MaroshCZ/Power-Supply-USB-C/STM32G0_USBPD_Sink_1.2/Application/app.c

/*
 * app.c
 *
 *  Created on: Apr 29, 2024
 *      Author: Jan Mareš
 */


#include "main.h"
#include "app.h"
#include "max7219.h"
#include "usbpd_def.h"
#include "usbpd_dpm_user.h"
#include "usbpd_pwr_user.h"
#include "usbpd_user_services.h"
#include "string.h"
#include "stdio.h"
#include "stdbool.h"
#include <stm32g0xx_ll_adc.h>

#include "usb_device.h"
#include "usbd_cdc_if.h"
#include <usbpd_trace.h>

int32_t fullyCompensatedVoltageV;
int32_t currentCompensatedVoltageV;
int32_t compVoltageV;
int32_t currentErrorV;
uint64_t term1V;
uint64_t term2V;
int64_t	voltageErrorV;
int32_t voltageErrorRoundedV;

int32_t BSP_USBPD_PWR_VBUSGetCurrentOCP(uint32_t Instance, int32_t *pCurrentOCP);
int32_t BSP_PWR_VBUSGetCurrentOCP(uint32_t PortId);

//Variables declaration
int dac_value = 500;

USBPD_DPM_SNKPowerRequestDetailsTypeDef powerRequestDetails;

__IO uint16_t aADCxConvertedValues[ADC_NUM_OF_SAMPLES] = {0};

//USB communication
uint8_t usb_buffer[64]; //in C, array automaticaly decays to pointer to first element uint8_t*

uint8_t *getUSBbuffer(void) {
	return usb_buffer;
}


//Initialize button event and time struct
SystemEvents_TypeDef systemEvents = {0};
BtnPressTimes_TypeDef btnPressTimes = {0};
volatile uint32_t debouncedPins = 0;  // Bitmask for tracking debounced buttons

//Init stateMachine struct
StateMachine_TypeDef stateMachine = {
		.currentState = STATE_INIT,
		.comState = STATE_CLOSED,
		.lockMode = UNLOCKED,
		.OCPMode = OCP_ENABLED,
		.lockLedState = LED_ON,
		.pwrMode = MODE_FIXED,
		.encoder = {
				.selDigit = 2,
				.increment = 10    // Default increment
			}
};

//Init SINKData struct
SINKData_HandleTypeDef SNK_data = {
	.voltageMin = 500, //initial min voltage
	.voltageSet = 500, //initial value to display
	.voltageMax = 500, //initial max voltage
	.currentSet = 1000, //initial value to display
	.awdgTresholdSet = 744, //set initial OCP to 1A
	.currentMin = 0,
	.currentOCPSet = 1000,
	.selMethod = PDO_SEL_METHOD_MAX_CUR,
	.hasAPDO = false,
	.srcProfiles[0].profileType = UNKNOWN,
	.requestOngoing = false
};

SINKData_HandleTypeDef *getSNK_data(void) {
	return &SNK_data;
}

// Define the pointer to the struct
SINKData_HandleTypeDef *dhandle = &SNK_data;
StateMachine_TypeDef *sm = &stateMachine;
SystemEvents_TypeDef *events = &systemEvents;


// Callback when ADC conversion is complete
void HAL_ADC_ConvCpltCallback(ADC_HandleTypeDef *hadc)
{
  //HAL_GPIO_TogglePin(LED_USER_GPIO_Port, LED_USER_Pin);
}

// Callback when ADWG2 (CH7 ISENSE) goes out of range
void HAL_ADCEx_LevelOutOfWindow2Callback(ADC_HandleTypeDef *hadc) {
	systemEvents.awdgEvent = true;
	//Disable output
	HAL_GPIO_WritePin(RELAY_ON_OFF_GPIO_Port, RELAY_ON_OFF_Pin, GPIO_PIN_RESET);
}

/**
 * Update ADC CH3 AWD Treshold
 * Possibility to update parameters on the fly (read more in HAL_ADC_AnalogWDGConfig declaration)
 * Full config and AWD init in main.c
 */
void Update_AWD_Thresholds(uint32_t low, uint32_t high, uint32_t adc_watchdog) {
		// Just update the thresholds for an already configured AWD
		ADC_AnalogWDGConfTypeDef AnalogWDGConfig = {0};
		AnalogWDGConfig.WatchdogNumber = adc_watchdog; // Specify which AWD you're updating
		AnalogWDGConfig.HighThreshold = high;
		AnalogWDGConfig.LowThreshold = low;
		if (HAL_ADC_AnalogWDGConfig(&hadc1, &AnalogWDGConfig) != HAL_OK)
		{
		    Error_Handler();
		}
}
/*
 * Initialization function
 */
void app_init(void){
	//TIM4 initialization
	HAL_TIM_Base_Start(&htim4);

	//TIM7 initialization
	LL_TIM_ClearFlag_UPDATE(TIM7); //Clear update flag on TIMER7
	LL_TIM_EnableIT_UPDATE(TIM7); //Enable interrupt generation when timer goes to max value and UPDATE event flag is set
	//LL_TIM_ClearFlag_UPDATE(TIM7); //Clear update flag on TIMER7

	//TIM14 initialization
	LL_TIM_DisableIT_UPDATE(TIM14); //Enable interrupt generation when timer goes to max value and UPDATE event flag is set
	LL_TIM_ClearFlag_UPDATE(TIM14); //Clear update flag on TIMER14

	//TIM14 initialization
	LL_TIM_DisableIT_UPDATE(TIM15); //Enable interrupt generation when timer goes to max value and UPDATE event flag is set
	LL_TIM_ClearFlag_UPDATE(TIM15); //Clear update flag on TIMER14

	//TIM3 initialization of encoder
	HAL_TIM_Encoder_Start_IT(&htim3, TIM_CHANNEL_ALL);
	uint32_t maxCounterValue = __HAL_TIM_GET_AUTORELOAD(&htim3); // Get the max value
	__HAL_TIM_SET_COUNTER(&htim3, maxCounterValue / 2); // Set the counter to half of the max value to avoid shift from 0 -> max value
	sm->encoder.curValue = __HAL_TIM_GET_COUNTER(&htim3)/4;
	sm->encoder.prevValue = sm->encoder.curValue;

	//Init DAC
	HAL_DAC_Start(&hdac1, DAC_CHANNEL_1);
	HAL_DAC_SetValue(&hdac1, DAC_CHANNEL_1, DAC_ALIGN_12B_R, dac_value);

	//Wait for hardware initialization and then turn DB to HIGH (according to TCPP01-M12 datasheet 6.5)
	HAL_Delay(200);
	HAL_GPIO_WritePin(DB_OUT_GPIO_Port, DB_OUT_Pin, GPIO_PIN_SET);

	//Calibrate and start ADC sensing with DMA
	HAL_ADCEx_Calibration_Start(&hadc1);
	HAL_ADC_Start_DMA(&hadc1, (uint32_t*)&aADCxConvertedValues, ADC_NUM_OF_SAMPLES);

	//Set initial OCP treshold
	Update_AWD_Thresholds(0, dhandle->awdgTresholdSet, ADC_ANALOGWATCHDOG_2); //~1A
	HAL_GPIO_WritePin(LED_USER_GPIO_Port, LED_USER_Pin, GPIO_PIN_SET);

	//Init 7 segment display
	max7219_Init( SEGMENT_DISP_INTENSIVITY );
	max7219_Decode_On();

	//HAL_GPIO_WritePin(OCP_RESET_GPIO_Port, OCP_RESET_Pin, GPIO_PIN_SET);
}


/*
 * Main loop function
 */
void app_loop(void) {
	// Process button events
	processSystemEvents();

	// Update lock/ocp LED
	updateLockLED();

	// Run the state machine
	runStateMachine();

	// Reset button states after processing
	stateMachine.outputBtnPressed = false;
	stateMachine.lockBtnPressed = false;
	stateMachine.lockBtnLongPressed = false;
	stateMachine.voltageCurrentBtnPressed = false;
	stateMachine.voltageCurrentBtnLongPressed = false;
	stateMachine.rotaryBtnPressed = false;
	stateMachine.encoderTurnedFlag = false;
	stateMachine.stateTimeoutFlag = false;
	stateMachine.periodicCheckFlag = false;
	stateMachine.encoderTurnedFlag = false;
	stateMachine.awdgTriggeredFlag = false;
}

/*
 * Main function for state machine
 */
void runStateMachine(void) {
	// Process events and transitions
	switch (sm->currentState) {
		case STATE_OFF:
			//handleOffState();
			break;
		case STATE_INIT:
			handleInitState();
			break;
		case STATE_IDLE:
			handleIdleState();
			break;
		case STATE_ACTIVE:
			handleActiveState();
			break;
		case STATE_ERROR:
			//handleErrorState();
			break;
		case STATE_SET_VALUES:
			handleSetValuesState();
			break;
		default:
			// Error handling
			sm->currentState = STATE_ERROR;
			//sm->errorCode = ERROR_INVALID_STATE;
			break;
	}

}

/*
 * Define Callbacks and ISR
 */

//BTN ISR to set event flags
void HAL_GPIO_EXTI_Falling_Callback(uint16_t GPIO_Pin) {
    if (GPIO_Pin == SW1_TOGGLE_I_V_Pin) {
        btnPressTimes.voltageCurrentBtn = HAL_GetTick();
        systemEvents.btnPressEvent = true;
        //EXTI->IMR1 &= ~(EXTI_IMR1_IM2);
    } else if (GPIO_Pin == SW2_DEBUG_BTN_Pin) {
        btnPressTimes.lockBtn = HAL_GetTick();
        systemEvents.btnPressEvent = true;
        //EXTI->IMR1 &= ~(EXTI_IMR1_IM4);
    } else if (GPIO_Pin == SW3_OFF_ON_Pin) {
        systemEvents.outputBtnEvent = true;
        //EXTI->IMR1 &= ~(EXTI_IMR1_IM1);
    } else if (GPIO_Pin == ENC_TOGGLE_UNITS_Pin) {
        systemEvents.rotaryBtnEvent = true;
        //EXTI->IMR1 &= ~(EXTI_IMR1_IM8);
    }

    // Store the pressed button in bitmask for tracking debounce
    debouncedPins |= GPIO_Pin;
    // Mask the interrupt for this button
    EXTI->IMR1 &= ~GPIO_Pin;

    // Start debounce timer
    TIM7->ARR = DEBOUNCE_TIME_MS;
    LL_TIM_SetCounter(TIM7, 0);
    LL_TIM_EnableCounter(TIM7);
}

/*
 * Define Callbacks and ISR
 */

//BTN ISR to set event flags
void HAL_GPIO_EXTI_Rising_Callback(uint16_t GPIO_Pin) {

	if (systemEvents.btnPressEvent == true) {
		uint32_t releaseTime = HAL_GetTick();

		// Decide between long/short presses
		if (GPIO_Pin == SW1_TOGGLE_I_V_Pin) {
			if ((releaseTime - btnPressTimes.voltageCurrentBtn) > 1000) {
				systemEvents.voltageCurrentBtnLongEvent = true;
			} else {
				systemEvents.voltageCurrentBtnEvent = true;
			}

		} else if (GPIO_Pin == SW2_DEBUG_BTN_Pin) {

			if ((releaseTime - btnPressTimes.lockBtn) > 1000) {
				systemEvents.lockBtnLongEvent = true;
			} else {
				systemEvents.lockBtnEvent = true;
			}
		} else {
			return;
		}

		// Start debounce timer
		TIM7->ARR = DEBOUNCE_TIME_MS;
		LL_TIM_SetCounter(TIM7, 0);
		LL_TIM_EnableCounter(TIM7);

		// Reset btnPressEvent
		systemEvents.btnPressEvent = false;

		// Store the pressed button in bitmask for tracking debounce
		debouncedPins |= GPIO_Pin;
		// Mask the interrupt for this button
		EXTI->IMR1 &= ~GPIO_Pin;
	}
}

//TIM capture callback
void HAL_TIM_IC_CaptureCallback(TIM_HandleTypeDef *htim) {
    if (htim->Instance == TIM3) {
    	systemEvents.encoderTurnEvent = true;
    }
}

/*
 * Timer7 interrupt routine for button debouncing
 */
void TIM7_ISR(void){
	//Clear TIM update flag and stop timer
	LL_TIM_ClearFlag_UPDATE(TIM7);
	LL_TIM_DisableCounter(TIM7);

	EXTI->IMR1 |= debouncedPins; // Unmask debounced pins
	EXTI->FPR1 = debouncedPins; // clear falling edge interrupt
	EXTI->RPR1 = debouncedPins; // clear rising edge interrupt

	// Reset the bitmask after unmasking
	debouncedPins = 0;

}

/*
 * TIM14 interrupt routine for periodic check inside states
 *
 */
void TIM14_ISR(void) {
	if (LL_TIM_IsActiveFlag_UPDATE(TIM14)) {
		// Clear the update interrupt flag
		LL_TIM_ClearFlag_UPDATE(TIM14);

		// Handle periodic check for ACTIVE state
		systemEvents.periodicCheckEvent = true;
		//Reset CNT value
		LL_TIM_SetCounter(TIM14, 0);

		//Start timer again
		LL_TIM_EnableCounter(TIM14);
	}
}

/*
 * TIM15 interrupt routine for timeouts of states
 *
 */
void TIM15_ISR(void) {
	if (LL_TIM_IsActiveFlag_UPDATE(TIM15)) {
		// Clear the update interrupt flag
		LL_TIM_ClearFlag_UPDATE(TIM15);

		// Handle periodic check for ACTIVE state
		systemEvents.stateTimeoutEvent = true;
		//Reset CNT value
		//LL_TIM_DisableCounter(TIM15);  // Stop the timer after timeout
	}
}

/*
 * Define Process functions
 */
// Process button events in the main loop (Convert hardware events into logical events)
void processButtonEvents(void) {
    if (events->outputBtnEvent) {
    	//Reset btn event flag
        events->outputBtnEvent = false;
        sm->outputBtnPressed = true;

    } else if (events->voltageCurrentBtnEvent) {
    	events->voltageCurrentBtnEvent = false;
    	sm->voltageCurrentBtnPressed = true;
    } else if (events->voltageCurrentBtnLongEvent) {
       	events->voltageCurrentBtnLongEvent = false;
       	sm->voltageCurrentBtnLongPressed = true;

       	// Toggle pwrMode
       	if (sm->pwrMode == MODE_FIXED) {
       		sm->pwrMode = MODE_APDO;
       	} else {
       		sm->pwrMode = MODE_FIXED;
       	}

    } else if (events->lockBtnEvent) {
    	events->lockBtnEvent = false;

    	if (sm->lockMode == UNLOCKED) {
    		sm->lockBtnPressed = true;
    		int isense_Vtrip_mV;
    		int isense_rawADCtrip;

			//Toggle OCP mode
			switch(sm->OCPMode) {
				case OCP_DISABLED:
					sm->OCPMode = OCP_ENABLED;

					//Set lock LED
					//HAL_GPIO_WritePin(LED_LOCK_GPIO_Port, LED_LOCK_Pin, GPIO_PIN_SET);

					//Update AWD limits
					isense_Vtrip_mV = (dhandle->currentSet *G_SENSE*R_SENSE_MOHMS)/1000; // mV  (mA * mOhms * Gain)
					isense_rawADCtrip = (isense_Vtrip_mV *4095) / VDDA_APPLI; //value for AWD treshold
					dhandle->awdgTresholdSet = isense_rawADCtrip;
					Update_AWD_Thresholds(0, isense_rawADCtrip, ADC_ANALOGWATCHDOG_2);
					break;
				case OCP_ENABLED:
					sm->OCPMode = OCP_DISABLED;

					//Reset lock LED
					//HAL_GPIO_WritePin(LED_LOCK_GPIO_Port, LED_LOCK_Pin, GPIO_PIN_RESET);

					//If OCP disabled by user, set it to source max current
					isense_Vtrip_mV = (dhandle->currentMax *G_SENSE*R_SENSE_MOHMS)/1000; // mV  (mA * mOhms * Gain)
					isense_rawADCtrip = (isense_Vtrip_mV *4095) / VDDA_APPLI; //value for AWD treshold
					dhandle->awdgTresholdSet = isense_rawADCtrip;
					Update_AWD_Thresholds(0, isense_rawADCtrip, ADC_ANALOGWATCHDOG_2);

					//__HAL_ADC_DISABLE_IT(&hadc1, ADC_IT_AWD2); can be also used to write bit but
					//only when ADSTART bit is cleared to 0 (this ensures that no conversion is ongoing).
					break;
			}
    	}

    } else if (events->lockBtnLongEvent) {
    	events->lockBtnLongEvent = false;
    	sm->lockBtnLongPressed = true;

    	if (sm->lockMode == LOCKED) {
    		sm->lockMode = UNLOCKED;

    		//Drive lock LED
    		//HAL_GPIO_WritePin(LED_LOCK_GPIO_Port, LED_LOCK_Pin, GPIO_PIN_RESET);
    		HAL_GPIO_WritePin(LED_USER_GPIO_Port, LED_USER_Pin, GPIO_PIN_RESET);


    		// Mask buttons except OUT
    		EXTI->IMR1 |= EXTI_IMR1_IM8; //unmask ENCbtn
    		EXTI->IMR1 |= EXTI_IMR1_IM2; //unmask SW1 I/V
    	} else {
    		sm->lockMode = LOCKED;

    		// Drive lock LED
    		//HAL_GPIO_WritePin(LED_LOCK_GPIO_Port, LED_LOCK_Pin, GPIO_PIN_SET);
    		HAL_GPIO_WritePin(LED_USER_GPIO_Port, LED_USER_Pin, GPIO_PIN_SET);

    		// Unmask buttons except OUT
    		EXTI->IMR1 &= ~(EXTI_IMR1_IM2); // mask SW1 I/V
    		EXTI->IMR1 &= ~(EXTI_IMR1_IM8); // mask ENCbtnt
    	}

    } else if (events->rotaryBtnEvent) {
    	// Reset btn event flag
    	events->rotaryBtnEvent = false;
		sm->rotaryBtnPressed = true;

    }
}

void processLockLedState(void) {
	 if (sm->OCPMode == OCP_DISABLED && sm->lockMode == UNLOCKED)
		sm->lockLedState = LED_OFF;
	else if (sm->OCPMode == OCP_ENABLED && sm->lockMode == UNLOCKED)
		sm->lockLedState = LED_ON;
	else if (sm->OCPMode == OCP_DISABLED && sm->lockMode == LOCKED)
		sm->lockLedState = LED_BLINK_SLOW;
	else if (sm->OCPMode == OCP_ENABLED && sm->lockMode == LOCKED)
		sm->lockLedState = LED_BLINK_FAST;
}


// Main system event processor that calls specialized handlers
void processSystemEvents(void) {
    // Process different event types using specialized functions
    processButtonEvents();

    // Process LockLed state based on decision matrix
    processLockLedState();


    // Process encoder actions
    if (events->encoderTurnEvent) {
    	sm->encoderTurnedFlag = true;
    	events->encoderTurnEvent = false;
    }
    // Process timeout of TIM15
    if (events->stateTimeoutEvent) {
		sm->stateTimeoutFlag= true;
		events->stateTimeoutEvent = false;
	}
    // Process periodic check of TIM14
	if (events->periodicCheckEvent) {
		sm->periodicCheckFlag= true;
		events->periodicCheckEvent = false;
	}
    // Process AWDG events
    if (events->awdgEvent) {
        events->awdgEvent = false;
        sm->awdgTriggeredFlag = true;
    }
}

/**
 * @brief Handle COM port status changes. Drive indicator LED and disable/enable button actions.
 *
 * @param host_com_port_open: is a bit value from CDC_Control_FS() case CDC_SET_CONTROL_LINE_STATE
 */
void handleCOMportstatus(uint8_t host_com_port_open){
	 static bool entryDone = false;
	 if (host_com_port_open == 1 && !entryDone) {
		 //Set COM state to OPEN
		 sm->comState = STATE_OPEN;
		 //Set default state timeout to 4000;
		 sm->timeoutCounter = 1500;

		 //Drive lock LED
		 //HAL_GPIO_WritePin(LED_LOCK_GPIO_Port, LED_LOCK_Pin, GPIO_PIN_SET);
		 HAL_GPIO_WritePin(LED_USER_GPIO_Port, LED_USER_Pin, GPIO_PIN_SET);

		 //Disable BTN interrupts
		 EXTI->IMR1 &= ~(EXTI_IMR1_IM2); //SW1
		 EXTI->IMR1 &= ~(EXTI_IMR1_IM4); //SW2
		 EXTI->IMR1 &= ~(EXTI_IMR1_IM1); //SW3
		 EXTI->IMR1 &= ~(EXTI_IMR1_IM8); //ENC btn

		 entryDone = true;

	 // Adding && entryDone is vital since it would otherwise entry this statement during debug
	 } else if (host_com_port_open == 0 && entryDone) {
		 sm->comState = STATE_CLOSED;

		 //Reset lock LED
		 //HAL_GPIO_WritePin(LED_LOCK_GPIO_Port, LED_LOCK_Pin, GPIO_PIN_RESET);
		 HAL_GPIO_WritePin(LED_USER_GPIO_Port, LED_USER_Pin, GPIO_PIN_RESET);

		 //Unmask exti line 1, 2 and 3
		 EXTI->IMR1 |= EXTI_IMR1_IM8; //unmask exti line 8
		 EXTI->IMR1 |= EXTI_IMR1_IM4; //unmask exti line 4
		 EXTI->IMR1 |= EXTI_IMR1_IM2; //unmask exti line 2
		 EXTI->IMR1 |= EXTI_IMR1_IM1; //unmask exti line 1

		 //If COM closed return savely to IDLE
		 sm->currentState = STATE_IDLE;

		 entryDone = false;
	 }
}

/**
 * @brief Clean specified delimiter from string array.
 *
 * @param input: Input string to be cleaned
 * @param output: Destination buffer for cleaned string
 * @param delimiter: Delimiter character(s) to be removed
 */
void cleanString(const char* input, char* output, const char* delimiter) {
    char temp[128];  // Temporary buffer for safe modification
    strncpy(temp, input, sizeof(temp) - 1);
    temp[sizeof(temp) - 1] = '\0';  // Ensure null-termination

    char* token = strtok(temp, delimiter);
    output[0] = '\0';  // Start with an empty output string

    while (token != NULL) {
        strcat(output, token);  // Append token to output
        token = strtok(NULL, delimiter);
    }
}


/**
 * @brief Process USB commands received from host.
 *
 * @param command: Pointer to command buffer
 * @param length: Length of the command
 *
 * Handles various commands for power supply control including:
 * - OCP (Over-Current Protection) enable/disable
 * - Voltage and current settings
 * - Output enable/disable
 * - Query commands for device status
 */
void processUSBCommand(uint8_t* command, uint32_t length)
{
	// Verify device has Adjustable Power Delivery Object capability
    // If only fixed profiles available, abort communication
	if (dhandle->hasAPDO == true) {
		sm->pwrMode = MODE_APDO;
	}
	else {
		return;
	}

	// Null-terminate the command to ensure string functions work properly
	command[length] = '\0';

	// Make a copy for tokenization to preserve original command
	char cmd_copy[64] = {0};
	strncpy(cmd_copy, (char*)command, sizeof(cmd_copy)-1);

	// Remove whitespace characters
	char cmd_trimmed[64];
	cleanString(cmd_copy, cmd_trimmed, " ");

	// Extract command part (everything up to ":" )
	char* cmd_part = strtok(cmd_trimmed, ":");
	char* params = NULL; // Will hold the parameter value after the colon

	// Parameters start after the delimiter
	if (cmd_part != NULL && strlen(cmd_part) < length) {
		params = strtok(NULL, ":");  // Get remaining part after ':'
	}

	//Create buffer for response mesage
	char response[64];

	// Process different command types
    if (strcmp(cmd_part, "OCP1") == 0)
    {
    	snprintf(response, sizeof(response), "OCP enabled\r\n");

        sm->OCPMode = OCP_ENABLED;

		// Update Analog Watchdog limits for over-current detection
		int isense_Vtrip_mV = (dhandle->currentSet *G_SENSE*R_SENSE_MOHMS)/1000; // mV  (mA * mOhms * Gain)
		int isense_rawADCtrip= (isense_Vtrip_mV *4095) / VDDA_APPLI; //value for AWD treshold
		Update_AWD_Thresholds(0, isense_rawADCtrip, ADC_ANALOGWATCHDOG_2);
    }
    else if (strcmp(cmd_part, "OCP0") == 0)
    {
    	snprintf(response, sizeof(response), "OCP disabled\r\n");

        sm->OCPMode = OCP_DISABLED;
        int isense_Vtrip_mV = (dhandle->currentMax *G_SENSE*R_SENSE_MOHMS)/1000; // mV  (mA * mOhms * Gain)
        int isense_rawADCtrip = (isense_Vtrip_mV *4095) / VDDA_APPLI; //value for AWD treshold
        dhandle->awdgTresholdSet = isense_rawADCtrip;
        Update_AWD_Thresholds(0, isense_rawADCtrip, ADC_ANALOGWATCHDOG_2);

        // Set Analog Watchdog to disabled threshold
		Update_AWD_Thresholds(0, OCP_DISABLED_HT, ADC_ANALOGWATCHDOG_2);
    }
    else if (strcmp(cmd_part, "VSET1") == 0)
    {
    	// Set voltage mode and update voltage setting
    	sm->rotaryBtnPressed = true;
    	sm->setValueMode = SET_VOLTAGE;

    	uint32_t voltage = atof(params)*100; // Convert float to uint (also V to centivolts)

    	// Validate voltage is within allowed range
    	if (dhandle->voltageMin < voltage && voltage < dhandle->voltageMax) {
    	   	dhandle->voltageSet = voltage; //save in centivolts
    		snprintf(response, sizeof(response), "Voltage set to new value: %lu.%02lu V\r\n", dhandle->voltageSet / 100, dhandle->voltageSet % 100);
    	} else {
    		snprintf(response, sizeof(response), "ERROR: Voltage out of bounds\r\n");
    	}
    }
    else if (strcmp(cmd_part, "TIMEOUT1") == 0)
	{
		uint32_t ms = atof(params)*1000; // Convert float to uint milliseconds

		// Validate timeout is within acceptable range (0-10 seconds)
		if (0 < ms && ms < 10000) {
			sm->timeoutCounter = ms;
			snprintf(response, sizeof(response), "Timeout set to new value: %lu.%03lu s\r\n", ms / 1000, ms % 1000);
		} else {
			snprintf(response, sizeof(response), "ERROR: Timeout out of bounds (0-10s)\r\n");
		}
	}
    else if (strcmp(cmd_part, "VSET1?") == 0)
	{
		// Convert mV to V and format as "XX.XX V"
		snprintf(response, sizeof(response), "Voltage is set to: %lu.%02lu V\r\n", dhandle->voltageSet / 100, dhandle->voltageSet % 100);
	}
    else if (strcmp(cmd_part, "ISET1") == 0)
	{
    	sm->rotaryBtnPressed = true;
    	sm->setValueMode = SET_CURRENT;

		uint32_t current = atof(params)*1000; // Convert float parameter to integer

		// Validate current is within allowed range
		if (dhandle->currentMin < current && current < dhandle->currentMax) {
			dhandle->currentSet = current; //save in mA
			snprintf(response, sizeof(response), "Current set to new value: %lu.%03lu A\r\n", dhandle->currentSet / 1000, dhandle->currentSet % 1000);
		} else {
			snprintf(response, sizeof(response), "ERROR: Current out of bounds\r\n");
		}

	}
    else if (strcmp(cmd_part, "ISET1?") == 0)
  	{
    	// Convert mA to A and format as "X.XXX A"
  		snprintf(response, sizeof(response), "Current is set to: %lu.%03lu A\r\n", dhandle->currentSet / 1000, dhandle->currentSet % 1000);
  	}
    else if (strcmp(cmd_part, "OUT0") == 0)
   	{
   		snprintf(response, sizeof(response), "Output disabled\r\n");
   	    // Simulate button press if device is in active state
   		if (sm->currentState == STATE_ACTIVE) {
   	   		sm->outputBtnPressed = true;
   		}
   	}
    else if (strcmp(cmd_part, "OUT1") == 0)
	{
		snprintf(response, sizeof(response), "Output enabled\r\n");

		// Simulate button press if device is in idle state
		if (sm->currentState == STATE_IDLE) {
			sm->outputBtnPressed = true;
		}
	}
    else if (strcmp(cmd_part, "VOUT1?") == 0)
   	{
    	uint32_t vol = BSP_PWR_VBUSGetVoltage(0); // [mV]
		uint32_t cur = BSP_PWR_VBUSGetCurrent(0); // [mA]

		//dhandle ->currentMeas = correctCurrentMeas(cur);
		dhandle ->currentMeas = correctCurrentMeas(cur);
		dhandle ->voltageMeas = vol;

		//Experimental function
		dhandle ->voltageMeasCorrected = correctVoltageMeas(dhandle->voltageMeas, dhandle ->currentMeas); //[mV]
    	// Query measured output voltage
   		snprintf(response, sizeof(response), "Measured output voltage: %lu.%02lu V\r\n", dhandle ->voltageMeasCorrected / 1000, dhandle->voltageMeasCorrected % 1000);
   	}
    else if (strcmp(cmd_part, "IOUT1?") == 0)
   	{
    	// Query measured output current
  		snprintf(response, sizeof(response), "Current is set to: %lu.%03lu A\r\n", dhandle->currentMeas / 1000, dhandle->currentMeas % 1000);
   	}
    else if (strcmp(cmd_part, "*IDN?") == 0)
	{
    	// Return device identification string
		snprintf(response, sizeof(response), "PPS-SINK-v0.2 (100W,21V,5A)\r\n");
	}
    else if (strcmp(cmd_part, "PROFILES?") == 0)
   	{
    	// Query available power profiles
    	bool printToCOM = true;
    	sourcecapa_limits(printToCOM);
   	}
    else
    {
    	// Handle unknown commands
        snprintf(response, sizeof(response), "Unknown command\r\n");
    }

    // Send response back to host
    CDC_Transmit_FS((uint8_t*)response, strlen(response));
}

/*
 * Define state Handle functions
 */
void handleInitState(void) {
    // Entry actions (if just entered this state)
    static bool entryDone = false;

    //=======================================================
	// ENTRY ACTIONS - Executed once when entering the state
	//=======================================================
    if (!entryDone) {
    	// Set the state entry time and timeout duration
		sm->stateEntryTime = HAL_GetTick();
		sm->timeoutCounter = 5000;  // 2 seconds timeout

        // Save state for return from temporary states
        sm->lastState = STATE_INIT;

        entryDone = true;
    }

    //==========================================================
	// DO ACTIONS - Executed every time the state is processed
	//==========================================================


    //=================================================
	// TRANSITION CHECKS - Check for state transitions
	//=================================================
    if (dhandle->srcProfiles[0].profileType != UNKNOWN) {
    	// Display maximal values
    	max7219_PrintIspecial(SEGMENT_2, dhandle->currentMax, 4);
    	max7219_PrintIspecial(SEGMENT_1, dhandle->voltageMax, 3);

    	// If APDO available set APDO mode
    	if (dhandle->hasAPDO == true) {
    		sm->pwrMode = MODE_APDO;
    	} else {
    		sm->pwrMode = MODE_FIXED;
    	}

    	// Check if the timeout has elapsed
		if (HAL_GetTick() - sm->stateEntryTime > sm->timeoutCounter) {
			//After initialization transition to IDLE state
			sm->currentState = STATE_IDLE;
			entryDone = false;
		}
    }

    //=================================================
    // EXIT ACTIONS - Things to be done during exit
    //=================================================
}

void handleIdleState(void) {
    // Entry actions (if just entered this state)
    static bool entryDone = false;

    //=======================================================
	// ENTRY ACTIONS - Executed once when entering the state
	//=======================================================
    if (!entryDone) {
        // Display set values
        max7219_PrintIspecial(SEGMENT_2, dhandle->currentSet, 4);
        max7219_PrintIspecial(SEGMENT_1, dhandle->voltageSet, 3);

        // Ensure output is off
        HAL_GPIO_WritePin(RELAY_ON_OFF_GPIO_Port, RELAY_ON_OFF_Pin, GPIO_PIN_RESET);

        // Save state for return from temporary states
        sm->lastState = STATE_IDLE;

        entryDone = true;
    }

    //=================================================
	// TRANSITION CHECKS - Check for state transitions
	//=================================================

    // Process events and transitions
    if (sm->outputBtnPressed) {
        sm->currentState = STATE_ACTIVE;
        entryDone = false;
    } else if (sm->rotaryBtnPressed) {
        sm->currentState = STATE_SET_VALUES;
        if (sm->comState == STATE_CLOSED) {
        	sm->timeoutCounter = 4000;  // 4 seconds timeout
        }
        sm->rotaryBtnPressed = false;
        entryDone = false;
    }

    //=================================================
    // EXIT ACTIONS - Things to be done during exit
    //=================================================
}

void handleActiveState(void) {
	// Entry actions (if just entered this state)
    static bool entryDone = false;
    static bool firstRequestDone = false;
    static int8_t periodicCheckFlagCounter = 0;


	//=======================================================
	// ENTRY ACTIONS - Executed once when entering the state
	//=======================================================

    if (!entryDone) {
        // Ensure output is off
        HAL_GPIO_WritePin(RELAY_ON_OFF_GPIO_Port, RELAY_ON_OFF_Pin, GPIO_PIN_SET);

        // Save state for return from temporary states
        sm->lastState = STATE_ACTIVE;

        // Initialize the periodic check timer
        TIM14->ARR = 500;
		LL_TIM_SetCounter(TIM14, 0); //set counter register value of timer 14 to 0
		LL_TIM_EnableIT_UPDATE(TIM14); // Enable update interrupt
		LL_TIM_EnableCounter(TIM14);

        entryDone = true;
    }

    //==========================================================
	// DO ACTIONS - Executed every time the state is processed
	//==========================================================

    //Periodic check to display measured values
    if (sm->periodicCheckFlag) {
    	uint32_t vol = BSP_PWR_VBUSGetVoltage(0); // [mV]
    	uint32_t cur = BSP_PWR_VBUSGetCurrent(0); // [mA]

    	//dhandle ->currentMeas = correctCurrentMeas(cur);
    	dhandle ->currentMeas = correctCurrentMeas(cur);
    	dhandle ->voltageMeas = vol;

    	//Experimental function
    	dhandle ->voltageMeasCorrected = correctVoltageMeas(dhandle->voltageMeas, dhandle ->currentMeas); //[mV]


    	//Display output voltage
    	max7219_PrintIspecial(SEGMENT_1, dhandle ->voltageMeasCorrected/10, 3); // divide voltage by 10 to get [cV]
    	//Display output current
    	max7219_PrintIspecial(SEGMENT_2, dhandle ->currentMeas, 4);

    	periodicCheckFlagCounter += 1;
    	if (!dhandle->requestOngoing) {
    		if (!firstRequestDone && periodicCheckFlagCounter >= 2){
    			correctOutputVoltage();
    			periodicCheckFlagCounter = 0;
    			firstRequestDone = true;
    		}

    		else if(periodicCheckFlagCounter >= 7){
    			periodicCheckFlagCounter = 0;

    			/*UNDER CONSTRUCTION*/
    			// Regulate output voltage
    			correctOutputVoltage();
    		}
    	}

    }

    //=================================================
	// TRANSITION CHECKS - Check for state transitions
	//=================================================
    if (sm->outputBtnPressed) {
        sm->currentState = STATE_IDLE;
        entryDone = false;
        firstRequestDone = false;
    } else if (sm->awdgTriggeredFlag) {
        sm->currentState = STATE_IDLE;
        entryDone = false;
        firstRequestDone = false;
    } else if (sm->rotaryBtnPressed) {
        sm->currentState = STATE_SET_VALUES;
        if (sm->comState == STATE_CLOSED) {
			sm->timeoutCounter = 4000;  // 4 seconds timeout
		}
        sm->rotaryBtnPressed = false;
        entryDone = false;
        firstRequestDone = false;
    }

    //=================================================
    // EXIT ACTIONS - Things to be done during exit
    //=================================================
    if (!entryDone) {
    	LL_TIM_DisableCounter(TIM14);
    }
}

void handleSetValuesState(void) {
    // Entry actions (if just entered this state)
    static bool entryDone = false;
    static bool showDigit = false;  // Start with digit shown

    //=======================================================
   	// ENTRY ACTIONS - Executed once when entering the state
   	//=======================================================

    if (!entryDone) {

    	// Display set values
        max7219_PrintIspecial(SEGMENT_2, dhandle->currentSet, 4);
        max7219_PrintIspecial(SEGMENT_1, dhandle->voltageSet, 3);

        // Initialize the periodic timer
		TIM14->ARR = 500;
		LL_TIM_SetCounter(TIM14, 0); //set counter register value of Timer14 to 0
		LL_TIM_EnableIT_UPDATE(TIM14); // Enable update interrupt
		LL_TIM_EnableCounter(TIM14);

		// Initialize the timeout timer
		LL_TIM_DisableCounter(TIM15);
		TIM15->ARR = sm->timeoutCounter;
		LL_TIM_SetCounter(TIM15, 0); //set counter register value of Timer15 to 0
		LL_TIM_EnableIT_UPDATE(TIM15); // Enable update interrupt
		LL_TIM_EnableCounter(TIM15);

        entryDone = true;
    }

    //==========================================================
	// DO ACTIONS - Executed every time the state is processed
	//==========================================================

    // User interaction - reset the timeout
	if (sm->rotaryBtnPressed || sm->encoderTurnedFlag || sm->voltageCurrentBtnPressed) {
		// Reset the timeout timer whenever there's user interaction
		LL_TIM_DisableCounter(TIM15);
		LL_TIM_SetCounter(TIM15, 0); //set counter register value of timer 14 to 0
		LL_TIM_EnableIT_UPDATE(TIM15); // Enable update interrupt
		LL_TIM_EnableCounter(TIM15);
	}

	// Process voltageCurrentBtn press
	if (sm->voltageCurrentBtnPressed) {
		//Reset flag
		sm->voltageCurrentBtnPressed = false;
		//Process
		if (sm->setValueMode == SET_VOLTAGE) {
			sm->setValueMode = SET_CURRENT;
		} else if (sm->setValueMode == SET_CURRENT) {
			sm->setValueMode = SET_VOLTAGE;
		}

		//Get values into debug trace
		char _str[60];
		uint32_t voltageADC = BSP_PWR_VBUSGetVoltage(0);
		uint32_t currentADC= BSP_PWR_VBUSGetCurrent(0);
		uint32_t currentOCP_ADC= BSP_PWR_VBUSGetCurrentOCP(0);

		// Use snprintf to limit the number of characters written
		int len = snprintf(_str, sizeof(_str), "VBUS:%lu mV, IBUS:%lu mA, IOCP:%lu mA", voltageADC, currentADC, currentOCP_ADC);

		USBPD_TRACE_Add(USBPD_TRACE_DEBUG, 0, 0, (uint8_t*)_str, strlen(_str));
	}

    //Process encoder press
    if (sm->rotaryBtnPressed) {
		//Decrement encoderPress value if higher than 4
		if (sm->encoder.selDigit > 1){
			sm->encoder.selDigit--;
		}
		else {
			sm->encoder.selDigit = 4;
		}

		//Choose addition value based on setValueMode
		int val;
		switch (sm->setValueMode){
			case SET_VOLTAGE:
				switch (sm->encoder.selDigit) {
				case 1: val = 2; break;
				case 2: val = 10; break;
				case 3: val = 100; break;
				case 4: val = 1000; break;
				}
			 break;
			//case SET_CURRENT:
			case SET_CURRENT:
				switch (sm->encoder.selDigit) {
				case 1: val = 5; break;
				case 2: val = 10; break;
				case 3: val = 100; break;
				case 4: val = 1000; break;
				}
			 break;
		}

		sm->encoder.increment = val;
    }


    //Process encoder turn
    if (sm->encoderTurnedFlag) {
		// Handle encoder pulse event
		int encoderVal = (TIM3 -> CNT) >> 2;

		sm->encoder.curValue= encoderVal;

		if (encoderVal != sm->encoder.prevValue){
			//Get the turn direction and save it
			sm->encoder.direction = (encoderVal < sm->encoder.prevValue) ? 1 : -1;

			//Save TIM3 CNT value to ValPrev
			sm->encoder.prevValue = encoderVal;

			//Set encoder Turn event flag
			sm->encoder.turnEvent = true;
		}
    }

    // Handle digit blinking based on current set mode
    if (sm->periodicCheckFlag) {
    	if (sm->setValueMode == SET_VOLTAGE) {
			max7219_BlinkDigit2(SEGMENT_1, dhandle->voltageSet, sm->encoder.selDigit, 3, showDigit);
			max7219_PrintIspecial(SEGMENT_2, dhandle->currentSet,4);
		} else { // SET_CURRENT
			max7219_BlinkDigit2(SEGMENT_2, dhandle->currentSet, sm->encoder.selDigit, 4, showDigit);
			max7219_PrintIspecial(SEGMENT_1, dhandle->voltageSet,3);
		}
    	//Toggle showDigit
    	showDigit = !showDigit;
    }

    // On turnEvent update voltage/current
	if (sm->encoder.turnEvent) {
		//Reset event flag
		sm->encoder.turnEvent = false;
		char _str[40];
		//Update displays
		switch (sm->setValueMode) {
			case SET_VOLTAGE:
				updateVoltage();
				//Print to debug !!calling it from inside updateVoltage() results in hardFault error!!
				sprintf(_str,"VBUS selected: %lu mV", dhandle->voltageSet * 10);
				USBPD_TRACE_Add(USBPD_TRACE_DEBUG, 0, 0, (uint8_t*)_str, strlen(_str));

				break;
			case SET_CURRENT:
				updateCurrent();
				//Print to debug !!calling it from inside updateVoltage() results in hardFault error!!
				sprintf(_str,"IBUS selected: %lu mA", dhandle->currentSet);
				USBPD_TRACE_Add(USBPD_TRACE_DEBUG, 0, 0, (uint8_t*)_str, strlen(_str));

				//IF OCP enabled update the tresholds
				if (sm->OCPMode == OCP_ENABLED) {
					//Update AWD limits
					int isense_Vtrip_mV = (dhandle->currentSet *G_SENSE*R_SENSE_MOHMS)/1000; // mV  (mA * mOhms * Gain)
					int isense_rawADCtrip= (isense_Vtrip_mV *4095) / VDDA_APPLI; //value for AWD treshold
					dhandle->awdgTresholdSet = isense_rawADCtrip;
					Update_AWD_Thresholds(0, isense_rawADCtrip, ADC_ANALOGWATCHDOG_2);
				}
				break;
		}
	}


	//=================================================
	// TRANSITION CHECKS - Check for state transitions
	//=================================================

    // If timeout from setValues make USB PD request with new values
    if (sm->stateTimeoutFlag) {

    	// BUILD AND SEND REQUEST //
		if (sm->pwrMode == MODE_APDO) {
			uint32_t cur = BSP_PWR_VBUSGetCurrent(0);
			dhandle->currentMeas = correctCurrentMeas(cur);
			// Compensate voltage for losses on shunt resistors
			uint32_t compVoltage = compensateVoltage(dhandle->currentMeas); // [cV]
			// Find index via USER_SERV_FindSRCIndex() based on requested values
			int indexSRCAPDO = USER_SERV_FindSRCIndex(0, &powerRequestDetails, compVoltage*10, dhandle->currentSet, dhandle ->selMethod);
			// Print to debug
			char _str[70];
			sprintf(_str,"APDO request: indexSRCPDO= %i, VBUS= %lu mV, Ibus= %lu mA", indexSRCAPDO, compVoltage*10, dhandle->currentSet);
			USBPD_TRACE_Add(USBPD_TRACE_DEBUG, 0, 0, (uint8_t*)_str, strlen(_str));
			// Send request to Policy Engine
			USBPD_DPM_RequestSRCPDO(0, indexSRCAPDO, compVoltage*10, dhandle->currentSet);
		}
		else if (sm->pwrMode == MODE_FIXED){
			// Use index from updateVoltage()
			int indexSRCPDO = dhandle->selectedProfile +1;
			// Print to debug
			char _str[70];
			sprintf(_str,"APDO request: indexSRCPDO= %i, VBUS= %lu mV, Ibus= %lu mA", indexSRCPDO, 10*dhandle->voltageSet, dhandle->currentSet);
			USBPD_TRACE_Add(USBPD_TRACE_DEBUG, 0, 0, (uint8_t*)_str, strlen(_str));
			// Send request to Policy Engine
			USBPD_DPM_RequestSRCPDO(0, indexSRCPDO, dhandle->voltageSet*10, dhandle->currentSet);
		}

    	//Return to last (previous) state
	    if (sm->lastState == STATE_IDLE) {
	        sm->currentState = STATE_IDLE;
	    } else if (sm->lastState == STATE_ACTIVE) {
	        sm->currentState = STATE_ACTIVE;
	    }
	    entryDone = false;
    }

    //=================================================
    // EXIT ACTIONS - Things to be done during exit
    //=================================================
	if (!entryDone) {
		LL_TIM_DisableCounter(TIM14);
	}

}

// Legacy function for handling INA301
/*
void sw2_lock_isr(void){
	//Mask unwanted button interrupts caused by debouncing on exti line 2 (PB2)
	EXTI->IMR1 &= ~(EXTI_IMR1_IM2);

	//Mask alert pin during setting the relay on/off
	//EXTI->IMR1 &= ~(EXTI_IMR1_IM6);

	//Set debouncing time in ms
	TIM7->ARR = 200;

	//Zero TIM7 counter and start counting
	LL_TIM_SetCounter(TIM7, 0); //set counter register value of timer 7 to 0
	LL_TIM_EnableCounter(TIM7); //start counting of timer 7

	char _str[60];

	if (outputState == OUTPUT_OFF_STATE)
			{
				outputState = OUTPUT_ON_STATE;
				//Mask unwanted button interrupts caused by debouncing on exti line 6 (PD6)
				EXTI->IMR1 &= ~(EXTI_IMR1_IM6);

				//Set debouncing time in 6 ms
				TIM14->ARR = 6;
				//Zero TIM7 counter and start counting
				LL_TIM_SetCounter(TIM14, 0); //set counter register value of timer 7 to 0
				LL_TIM_EnableCounter(TIM14); //start counting of timer 7

				//put OCP to transparent mode so any alert during on/off is cleared
				//HAL_GPIO_WritePin(OCP_RESET_GPIO_Port, OCP_RESET_Pin, GPIO_PIN_RESET);
				HAL_GPIO_WritePin(RELAY_ON_OFF_GPIO_Port, RELAY_ON_OFF_Pin, GPIO_PIN_SET);
				// Use snprintf to limit the number of characters written
				int len = snprintf(_str, sizeof(_str), "--------Output Disabled--------");

			}
			else {
				outputState = OUTPUT_OFF_STATE;
				HAL_GPIO_WritePin(RELAY_ON_OFF_GPIO_Port, RELAY_ON_OFF_Pin, GPIO_PIN_RESET);
				// Use snprintf to limit the number of characters written
				int len = snprintf(_str, sizeof(_str), "--------Output Enabled--------");

				//Display voltage
				max7219_PrintIspecial(SEGMENT_1,dhandle->voltageSet, 3);
				//Display current
				max7219_PrintIspecial(SEGMENT_2, dhandle->currentSet, 4);
			}

	//HAL_GPIO_TogglePin(RELAY_ON_OFF_GPIO_Port, RELAY_ON_OFF_Pin);
	//Get Voltage level into TRACE
	USBPD_TRACE_Add(USBPD_TRACE_DEBUG, 0, 0, (uint8_t*)_str, strlen(_str));
}*/

/**
  * @brief  Extract source (adapter) capabilities and save them to SNKData_handle. If required print those capa. also to COM
  * @param  printToCom: Bool for specifying to print/not print to COM
  * @retval None
  * source: demo_disco.c Display_sourcecapa_menu_nav
  */
void sourcecapa_limits(bool printToCOM)
{
	// Entry actions (if just entered this state)
	static bool firstEntry = true;

	uint8_t _max = DPM_Ports[0].DPM_NumberOfRcvSRCPDO;
	uint8_t _start = 0;
	//SINKData_HandleTypeDef *dhandle = &SNK_data;
	dhandle->numProfiles = _max;
	static char all_profiles[500] = {0}; // Buffer for all profiles
	uint16_t offset = 0; // Position tracker in the all_profiles buffer

	// Clear the buffer at the start
	memset(all_profiles, 0, sizeof(all_profiles));

	for(int8_t index=_start; index < _max; index++)
	{
		char _str[50] = {0};

		switch(DPM_Ports[0].DPM_ListOfRcvSRCPDO[index] & USBPD_PDO_TYPE_Msk)
		{
			case USBPD_PDO_TYPE_FIXED :
			{
				uint32_t maxcurrent = ((DPM_Ports[0].DPM_ListOfRcvSRCPDO[index] & USBPD_PDO_SRC_FIXED_MAX_CURRENT_Msk) >> USBPD_PDO_SRC_FIXED_MAX_CURRENT_Pos)*10;
				uint32_t maxvoltage = ((DPM_Ports[0].DPM_ListOfRcvSRCPDO[index] & USBPD_PDO_SRC_FIXED_VOLTAGE_Msk) >> USBPD_PDO_SRC_FIXED_VOLTAGE_Pos)*50;
				sprintf((char*)_str, "FIXED:%2dV %2d.%dA \r\n", (int)(maxvoltage/1000), (int)(maxcurrent/1000), (int)((maxcurrent % 1000) /100));

				// Extract min and max values
				if (maxvoltage > dhandle->voltageMax*10) {
					dhandle -> voltageMax = (int)maxvoltage/10;
				}
				if (maxcurrent > dhandle->currentMax) {
					dhandle -> currentMax = (int)maxcurrent;
				}

				// Copy profiles to SNK data
				if (firstEntry) {
					if ((maxvoltage/1000 * maxcurrent/1000) <= 100) {
						dhandle->srcProfiles[index].voltageMax = maxvoltage/10; //save in centivolts
						dhandle->srcProfiles[index].currentMax = maxcurrent; //save in mA
						dhandle->srcProfiles[index].profileType = FIXED;
					}
				}

				break;
			}
			case USBPD_PDO_TYPE_BATTERY :
			{
			}
			break;
			case USBPD_PDO_TYPE_VARIABLE :
			{
				uint32_t maxvoltage = ((DPM_Ports[0].DPM_ListOfRcvSRCPDO[index] & USBPD_PDO_SRC_VARIABLE_MAX_VOLTAGE_Msk) >> USBPD_PDO_SRC_VARIABLE_MAX_VOLTAGE_Pos) * 50;
				uint32_t minvoltage = ((DPM_Ports[0].DPM_ListOfRcvSRCPDO[index] & USBPD_PDO_SRC_VARIABLE_MIN_VOLTAGE_Msk) >> USBPD_PDO_SRC_VARIABLE_MIN_VOLTAGE_Pos) * 50;
				uint32_t maxcurrent = ((DPM_Ports[0].DPM_ListOfRcvSRCPDO[index] & USBPD_PDO_SRC_VARIABLE_MAX_CURRENT_Msk) >> USBPD_PDO_SRC_VARIABLE_MAX_CURRENT_Pos) * 10;
				sprintf((char*)_str, "V:%2d.%1d-%2d.%1dV %d.%dA \r\n", (int)(minvoltage/1000),(int)(minvoltage/100)%10, (int)(maxvoltage/1000),(int)(maxvoltage/100)%10, (int)(maxcurrent/1000), (int)((maxcurrent % 1000) /100));
			}
			break;
			case USBPD_PDO_TYPE_APDO :
			{
				uint32_t minvoltage = ((DPM_Ports[0].DPM_ListOfRcvSRCPDO[index] & USBPD_PDO_SRC_APDO_MIN_VOLTAGE_Msk) >> USBPD_PDO_SRC_APDO_MIN_VOLTAGE_Pos) * 100;
				uint32_t maxvoltage = ((DPM_Ports[0].DPM_ListOfRcvSRCPDO[index] & USBPD_PDO_SRC_APDO_MAX_VOLTAGE_Msk) >> USBPD_PDO_SRC_APDO_MAX_VOLTAGE_Pos) * 100;
				uint32_t maxcurrent = ((DPM_Ports[0].DPM_ListOfRcvSRCPDO[index] & USBPD_PDO_SRC_APDO_MAX_CURRENT_Msk) >> USBPD_PDO_SRC_APDO_MAX_CURRENT_Pos) * 50;
				sprintf((char*)_str, "APDO:%2d.%1d-%2d.%1dV %d.%dA \r\n",(int) (minvoltage/1000),(int)(minvoltage/100)%10, (int)(maxvoltage/1000),(int)(maxvoltage/100)%10, (int)(maxcurrent/1000), (int)((maxcurrent % 1000) /100));

				// Set hasAPDO flag
				dhandle->hasAPDO = true;

				// Extract min and max values (since APDOs are last it will rewrite FIXED values,
				// this is what we want since if APDO is present the sink will default to APDO mode
				if (minvoltage < dhandle->voltageMin*10) {
					dhandle -> voltageMin = (int)minvoltage/10;
				}
				if (maxvoltage > dhandle->voltageMax*10) {
					dhandle -> voltageMax = (int)maxvoltage/10;
				}
				if (maxcurrent > dhandle->currentMax) {
					dhandle -> currentMax = (int)maxcurrent;
				}

				// Copy profiles to SNK data
				if (firstEntry) {
					if ((maxvoltage/1000 * maxcurrent/1000) <= 100) {
						dhandle->srcProfiles[index].voltageMin = minvoltage/10; //save in centivolts
						dhandle->srcProfiles[index].voltageMax = maxvoltage/10; //save in centivolts
						dhandle->srcProfiles[index].currentMax = maxcurrent; //save in mA
						dhandle->srcProfiles[index].profileType = APDO;
					}
				}
			}
			break;
			default :
			{
				sprintf((char*)_str,"Unknown Source PDO \r\n");
				break;
			}

			}
			// Add current profile to the buffer with bounds checking
			uint16_t len = strlen(_str);
			if (offset + len < sizeof(all_profiles) - 1) {
				memcpy(all_profiles + offset, _str, len);
				offset += len;
		} //switch end

	} //for end

	// Ensure null termination
	all_profiles[offset] = '\0';

	// Send all profiles at once
	if (printToCOM && offset > 0) {
		CDC_Transmit_FS((uint8_t*)all_profiles, offset);
	}

	// Clear first entry flag
	firstEntry = false;
}


// Helper function to update voltage
void updateVoltage(void) {

	switch (sm -> pwrMode) {
		case MODE_FIXED:
		{
				// Create helper index variable
				int8_t index = dhandle->selectedProfile + sm->encoder.direction;

				// Find index of next FixedPDO based on encoder turn direction (They are always at the beginning of Profiles list)
				if ((0 <= index) && (index <= dhandle->numProfiles -1)) {
					if (dhandle->srcProfiles[index].profileType != FIXED) {
						index = 0; //we are out of fixed profiles that are defined at beginning, return to 0
					}
				} else if (index < 0) {
					// Search for the last FixedPDO
					for (index = dhandle->numProfiles -1; index >= 0; index--) {
						if (dhandle->srcProfiles[index].profileType == FIXED) {
							break;
						}
					}
				} else if (index >= dhandle->numProfiles) {
					index = 0;
				}

				dhandle->selectedProfile = index;

				// Apply parameters of found srcProfile index
				dhandle->voltageMax = dhandle->srcProfiles[index].voltageMax;
				dhandle->voltageMin = dhandle->voltageMax;
				dhandle->voltageSet = dhandle->voltageMax;
				dhandle->currentMax = dhandle->srcProfiles[index].currentMax;

				// If new voltage has lower current limit adjust accordingly
				if (dhandle->currentSet > dhandle->currentMax) {
					dhandle->currentSet = dhandle->currentMax;
				}
		}
			break;

		case MODE_APDO:
		{
			//Get direction of encoder turning
			int voltageTemp = dhandle->voltageSet;
			voltageTemp += sm->encoder.direction * sm->encoder.increment;

			// Extract total bounds of APDO
			for (int8_t i = 0; i <= dhandle->numProfiles-1; i++) {
				if (dhandle->srcProfiles[i].profileType == APDO) {
					if (dhandle->srcProfiles[i].voltageMin < dhandle->voltageMin) {
						dhandle->voltageMin = dhandle->srcProfiles[i].voltageMin;
					}
					if (dhandle->srcProfiles[i].voltageMax > dhandle->voltageMax) {
						dhandle->voltageMax = dhandle->srcProfiles[i].voltageMax;
					}
					if (dhandle->srcProfiles[i].currentMax > dhandle->currentMax) {
						dhandle->currentMax = dhandle->srcProfiles[i].currentMax;
					}
				}

			}

			// If required temp value is within limits, assign it to voltage else assign limits
			if (dhandle->voltageMin <= voltageTemp && voltageTemp <= dhandle->voltageMax) {
				dhandle->voltageSet = voltageTemp; //asign new voltage
			} else {
				return;
			}
			// Update index
			int8_t index = dhandle->selectedProfile;
			// Search if there is APDO with higher current capability and satisfies voltageSet
			for (int8_t i = dhandle->numProfiles-1; i >= 0; i--) {
				if (dhandle->srcProfiles[i].profileType == APDO) {
					if (dhandle->voltageSet < dhandle->srcProfiles[i].voltageMax) {
						//update max current
						dhandle->currentMax = dhandle->srcProfiles[i].currentMax;

						//store profile index
						index = i;
					} else {
						break;
					}
				} else {
					break;
				}
			}

			dhandle->selectedProfile = index;

			// If new voltage has lower current limit adjust accordingly
			if (dhandle->currentSet > dhandle->currentMax) {
				dhandle->currentSet = dhandle->currentMax;
			}
			// dhandle->selectedProfile = USER_SERV_FindSRCIndex(0, &powerRequestDetails, compVoltage*10, dhandle->currentSet, dhandle ->selMethod);
		}
			break;
		default:
		{
		}
			break;
	}


	//Print selected voltage to disp, decimal at digit 3
	max7219_PrintIspecial(SEGMENT_1, dhandle->voltageSet, 3);
}

// Helper function to update current
void updateCurrent(void) {
	//Get direction of encoder turning
	int currentTemp = dhandle->currentSet;
	currentTemp += sm->encoder.direction * sm->encoder.increment;

	// If required temp value is within limits, assign it to voltage else assign limits
	if (dhandle->currentMin <= currentTemp && currentTemp <= dhandle->currentMax) {
		dhandle->currentSet = currentTemp; //asign new voltage
	} else {
		return;
	}

	//Print selected voltage to disp, decimal at digit 3
	max7219_PrintIspecial(SEGMENT_2, dhandle->currentSet, 4);
}

// Helper function to update OCP current (INA 301)
void updateCurrentOCP(void) {
	//Get direction of encoder turning
	int currentTemp = dhandle->currentOCPSet;
	currentTemp += sm->encoder.direction * sm->encoder.increment;

	//If required temp value is within limits, assign it to voltage
	if ( (dhandle->currentMin <= currentTemp) && (currentTemp <= (dhandle->currentMax + 300)) ) {
		dhandle->currentOCPSet = currentTemp;
	} else {
		//currentOCPTemp = currentOCP;
	}

	int V_TRIP = (dhandle->currentOCPSet * R_OCP_MOHMS * G_OCP)/1000; // mV (mA * mOhms * Gain)
	//Convert DAC_OUT voltage to 12B resolution
	int dac_value = (V_TRIP *4095) / VDDA_APPLI;//__LL_ADC_DIGITAL_SCALE(LL_ADC_RESOLUTION_12B);
	//Write output with DAC..
	HAL_DAC_SetValue(&hdac1, DAC_CHANNEL_1, DAC_ALIGN_12B_R, dac_value);

	//Print selected voltage to disp, decimal at digit 3
	max7219_PrintIspecial(SEGMENT_2, dhandle->currentOCPSet, 4);
}

// Make voltage correction for the voltage drop in system.
// Purpose of this compensation is approximation of the voltageDrop
// based on measured current before the request is made.
// Since it is based on currentMeas, it works only when OUT is enabled.
// This should give us Uout close to user desired Uset.
// Characteristic was obtained from PinePower 65W adapter.
uint32_t compensateVoltage(uint32_t measuredCurrent) {
	// Using the formula: voltageDrop = 0.2942x * x - 49.8529
	// To avoid floats, convert to int: (2942 * x - 498530 + 5000) / 10000
	// The + 5000 ensures proper rounding to nearest integer
	uint32_t a = 2942;
	uint32_t b = 498529;
	int32_t voltageDrop = (a*dhandle->currentMeas - b + 5000)/10000;
	uint32_t compVoltage;

	// Below 150mA the voltageDrop might be negative
	if (dhandle->currentMeas > 180 && voltageDrop > 0){
		compVoltage = roundToNearest20mV(dhandle->voltageSet*10 + voltageDrop) / 10; //divide by 10 to get [cV]
	}
	else {
		compVoltage = dhandle->voltageSet; // [cV]
	}

	// If corrected value is within limits proceed, else ask for mask Voltage
	compVoltageV = compVoltage;
	return (compVoltage > dhandle->voltageMax) ? dhandle->voltageMax : compVoltage;
}

int32_t roundToNearest20mV(int32_t valueInMv) {

	int32_t sign = (valueInMv < 0) ? -1 : 1;
	int32_t absValue = abs(valueInMv);

	if (absValue % 20 >= 10 && sign == -1) {

	}
	int32_t roundedValueInMv = absValue - (absValue % 20) + ( (absValue % 20 >= 10 && sign == -1) ? 20 : 0);

    return sign*roundedValueInMv;
}

/**
  * @brief  Current measurement correction
  * @param  measuredCurrent: Measured current with ADC [mA]
  * @retval correctedCurrent [mA]
  */
int32_t correctCurrentMeas(uint32_t measuredCurrent) {
	// Using the formula: er = 0.0065 * current + 7.5956 (measured on PinePower)
	// Skew of correction was slightly changed to 0.0059, to better match with other adapters
	// To avoid floats, convert to int: (59 * current + 75956 + 5000) / 10000
	// The + 5000 ensures proper rounding to nearest integer
	uint32_t a = 59;		// Coefficient: 0.059 * 10000
	uint32_t b = 75956;    // Coefficient: 7.9556 * 10000
	int32_t currentError = (a * measuredCurrent + b + 5000) / 10000;
	int32_t correctedCurrent = (int32_t)measuredCurrent - currentError;
	if (correctedCurrent > 3){
		return correctedCurrent;
	}
	else {
		return 0;
	}
}

/**
 * @brief  Corrects voltage measurement to compensate for system errors.
 * Performs two-step correction:
 * 1. Current-dependent compensation: Accounts for losses in shunt resistor, relay and path
 *    Using formula: error = 0.0721 * voltage - 17.279 [mV]
 * 2. Voltage-dependent compensation: Corrects for voltage divider and ADC reference errors
 *    Using formula: error = 0.0000002 * voltage^2 - 0.00989229 * voltage + 107.30097708 [mV]
 *
  * @param  measuredVoltage: Measured voltage on voltage divider with ADC [mV]
  * @retval correctedVoltage: Corrected output voltage [mV]
  */
int32_t correctVoltageMeas(uint32_t measuredVoltage, uint32_t measuredCurrent) {
	// Step 1: Current-dependent compensation
	// Using the formula: er = 0.0721 * current - 17.279 [mV] (measured on PinePower)
	// Integer implementation: (721 * current - 172790 + 5000) / 10000
	int32_t a = 721;		// Coefficient: 0.0721 * 10000
	int32_t b = 172790;    // Coefficient: 17.279 * 10000
	int32_t voltageLoadLoss;
	if (measuredCurrent >= 1) {
		voltageLoadLoss = (a * (int32_t)measuredCurrent - b + 5000) / 10000;
	}
	else {
		voltageLoadLoss = -17; // -b/10000
	}
	currentErrorV = voltageLoadLoss;
	int64_t loadCorrectedVoltage = measuredVoltage - voltageLoadLoss;
	currentCompensatedVoltageV = loadCorrectedVoltage;

	// Compensation in dependence of voltage
	// Using the formula: er = 0.00000020x^2 - 0.00989229x + 107.30097708 (measured on PinePower)
	// To avoid floats, convert to int: (2x^2 - 98923 + 1073009771) / 10000
	int32_t e = 2;   			// Coefficient: 0.0000002 * 10000 = 2/1000
	int32_t f = 99;		// Coefficient: 0.00989229 * 10000
	int64_t g = 1073010;    // Coefficient: 107.30097708 * 10000

	int64_t term1 = (e * (loadCorrectedVoltage/100) * loadCorrectedVoltage/10);
	int64_t term2 = f * loadCorrectedVoltage;
	int64_t term3 = term1 - term2 + g;
	int64_t voltageError = term3 / 10000;
	term1V = term1;
	term2V = term2;
	voltageErrorV = voltageError;

	uint32_t fullyCompensatedVoltage = loadCorrectedVoltage - voltageError;
	fullyCompensatedVoltageV = fullyCompensatedVoltage;

	return fullyCompensatedVoltage;
}

void correctOutputVoltage(void) {
	static bool firstEntry = true;
	static uint32_t voltageSetPrevious;

	if (sm->pwrMode == MODE_APDO && sm->currentState == STATE_ACTIVE) {

		dhandle->voltageError = fullyCompensatedVoltageV - dhandle->voltageSet*10; // [mV = mV - cV*10]

		if (abs(dhandle->voltageError) > 30) {
			//round toward zero in 20mV steps
			int32_t voltageErrorRounded = roundToNearest20mV(dhandle->voltageError);  // [mV]
			voltageErrorRoundedV = voltageErrorRounded;

			if (firstEntry || voltageSetPrevious!= dhandle->voltageSet) {
				dhandle->correctedRequestVoltage += dhandle->voltageSet - voltageSetPrevious; //dhandle->voltageSet - voltageErrorRounded/(int32_t)10; // [cV = cV - mV/10]
				firstEntry = false;
			}
			else {
				dhandle->correctedRequestVoltage = dhandle->correctedRequestVoltage - voltageErrorRounded/(int32_t)10; // [cV = cV - mV/10]
			}


			if (dhandle->correctedRequestVoltage >= dhandle->voltageMax) {
				dhandle->correctedRequestVoltage = dhandle->voltageMax;
			}
			else if (dhandle->correctedRequestVoltage <= dhandle->voltageMin) {
				dhandle->correctedRequestVoltage = dhandle->voltageMin;
			}
			int indexSRCAPDO = USER_SERV_FindSRCIndex(0, &powerRequestDetails, dhandle->correctedRequestVoltage*10, dhandle->currentSet, dhandle ->selMethod);
			// Print to debug
			char _str[100];
			sprintf(_str,"APDO correction request: indexSRCPDO= %i, setVBUS= %lu mV, corVBUS= %lu mV, Ibus= %lu mA", indexSRCAPDO, 10*dhandle->voltageSet, dhandle->correctedRequestVoltage*10, dhandle->currentSet);
			USBPD_TRACE_Add(USBPD_TRACE_DEBUG, 0, 0, (uint8_t*)_str, strlen(_str));
			USBPD_DPM_RequestSRCPDO(0, indexSRCAPDO, dhandle->correctedRequestVoltage*10, dhandle->currentSet);

		}

		voltageSetPrevious = dhandle -> voltageSet;
	}
}

void updateLockLED(void) {
    static uint32_t lastToggle = 0;
    uint32_t now = HAL_GetTick();  // nebo millis()

    switch (sm->lockLedState) {
        case LED_OFF:
            HAL_GPIO_WritePin(LED_LOCK_GPIO_Port, LED_LOCK_Pin, GPIO_PIN_RESET);
            break;
        case LED_ON:
            HAL_GPIO_WritePin(LED_LOCK_GPIO_Port, LED_LOCK_Pin, GPIO_PIN_SET);
            break;
        case LED_BLINK_SLOW:
            if (now - lastToggle >= 500) {
                HAL_GPIO_TogglePin(LED_LOCK_GPIO_Port, LED_LOCK_Pin);
                lastToggle = now;
            }
            break;
        case LED_BLINK_FAST:
            if (now - lastToggle >= 150) {
                HAL_GPIO_TogglePin(LED_LOCK_GPIO_Port, LED_LOCK_Pin);
                lastToggle = now;
            }
            break;
    }
}
